thamirislibard/thrust-stand-calibration/src/0.Images/electromagnet_damping_34V_closer.png

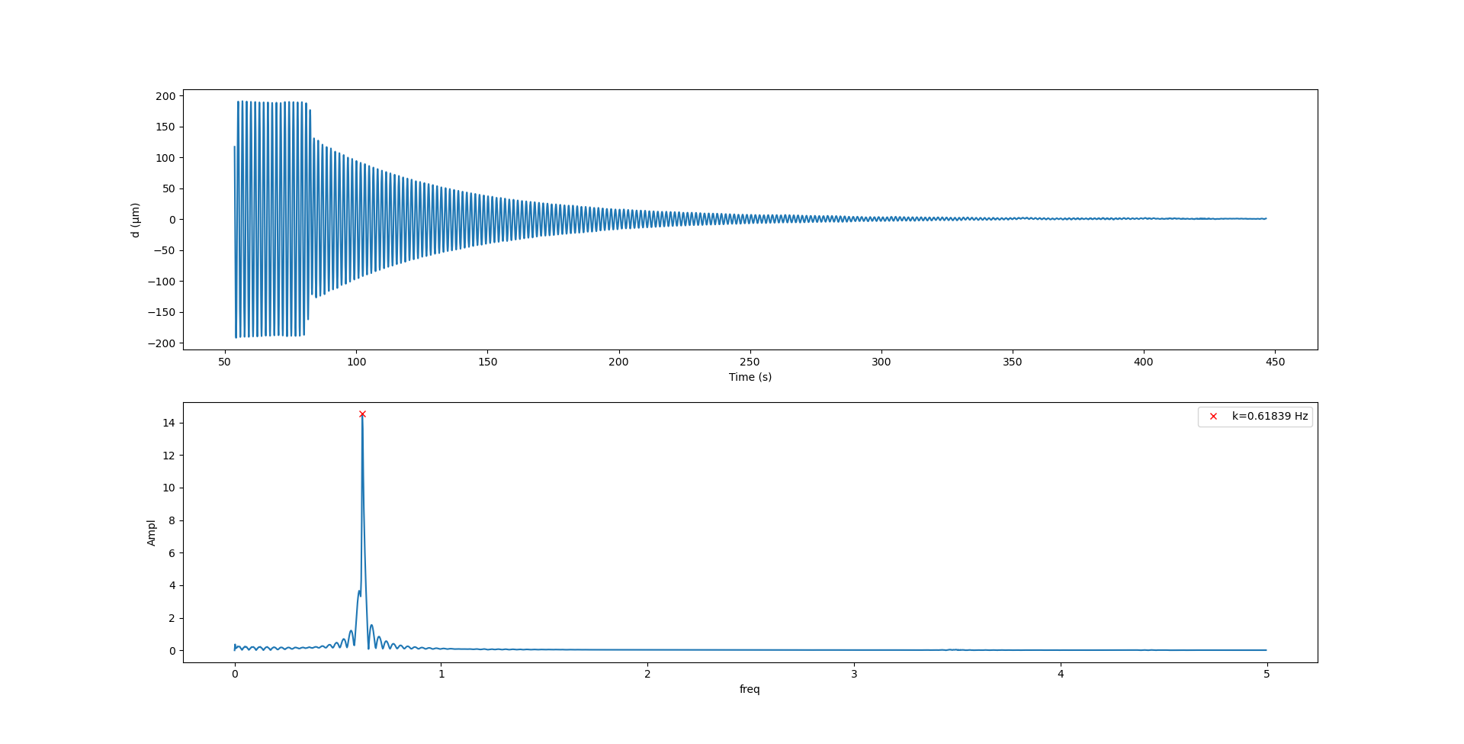
src/0.Images/electromagnet_damping_34V_closer.png
