thamirislibard/thrust-stand-calibration/src/0.Images/electromagnet_damping_34V_evencloser_2.png

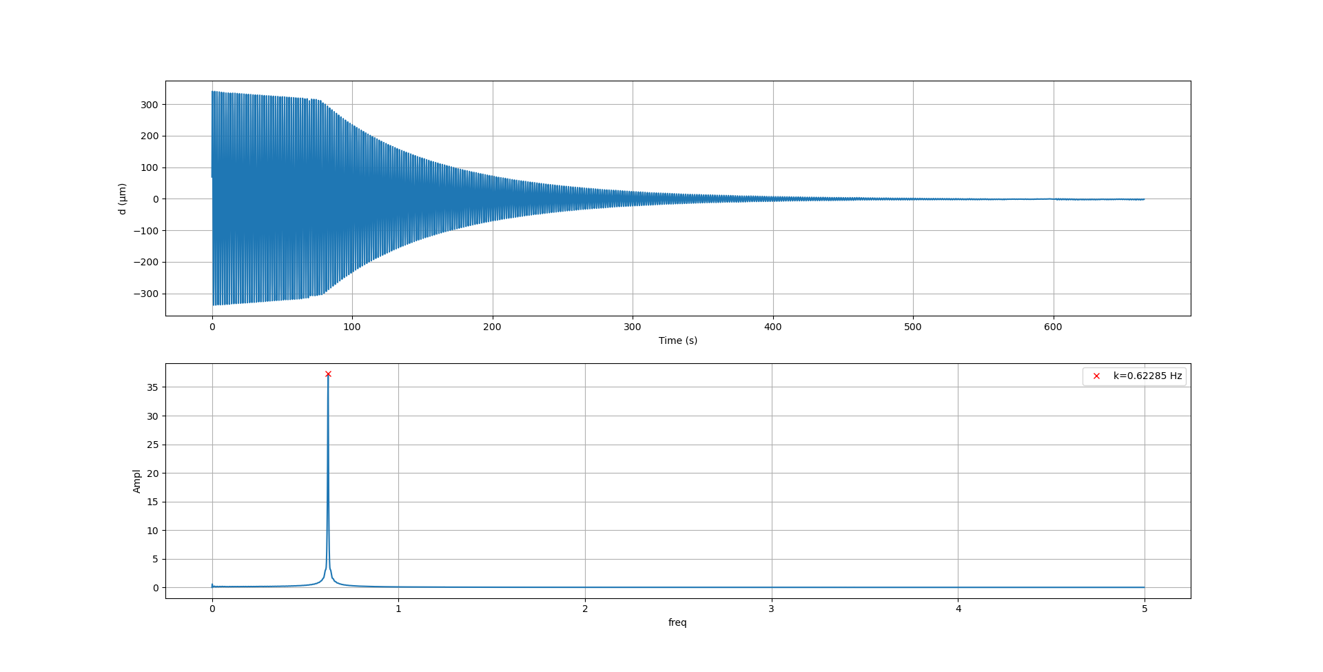
src/0.Images/electromagnet_damping_34V_evencloser_2.png
