thamirislibard/thrust-stand-calibration/src/0.Images/Static_deflection1_5mm.png

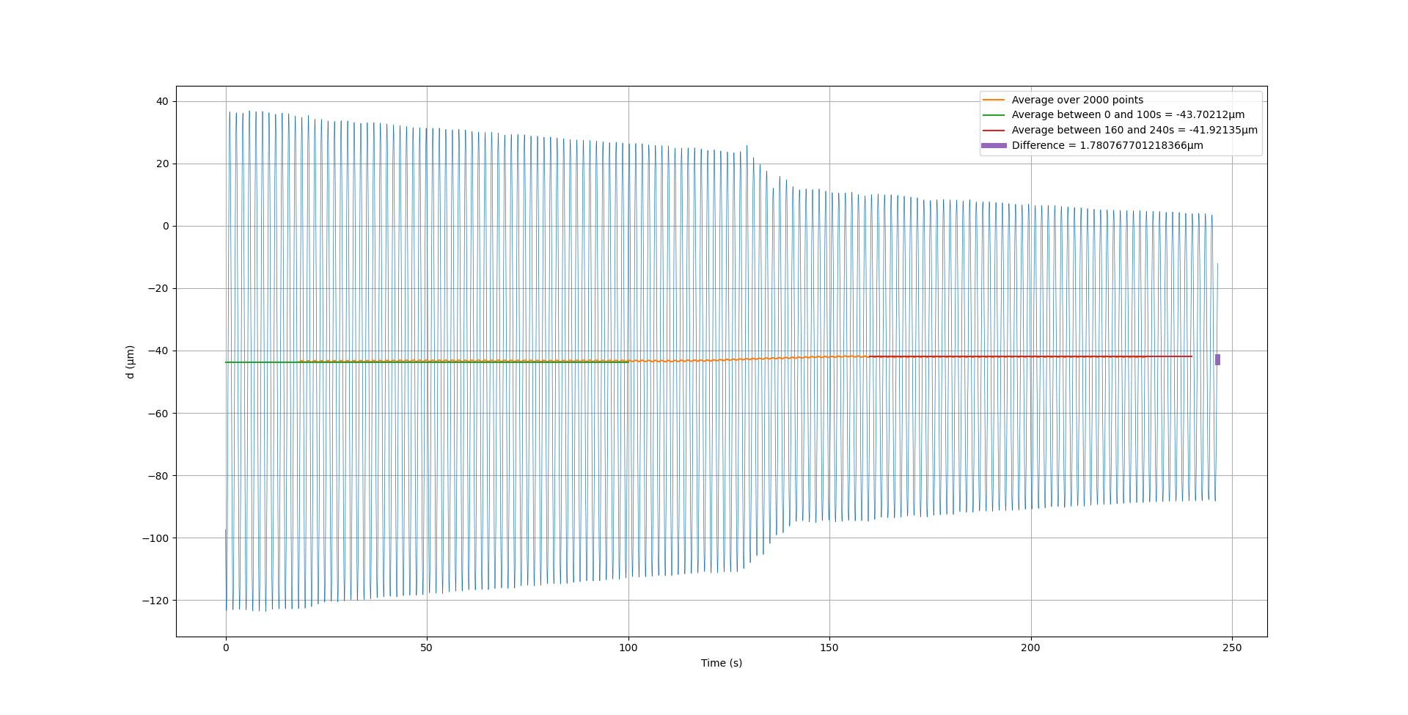
src/0.Images/Static_deflection1_5mm.png
