thamirislibard/thrust-stand-calibration/src/0.Images/Static_deflection1_15mm.png

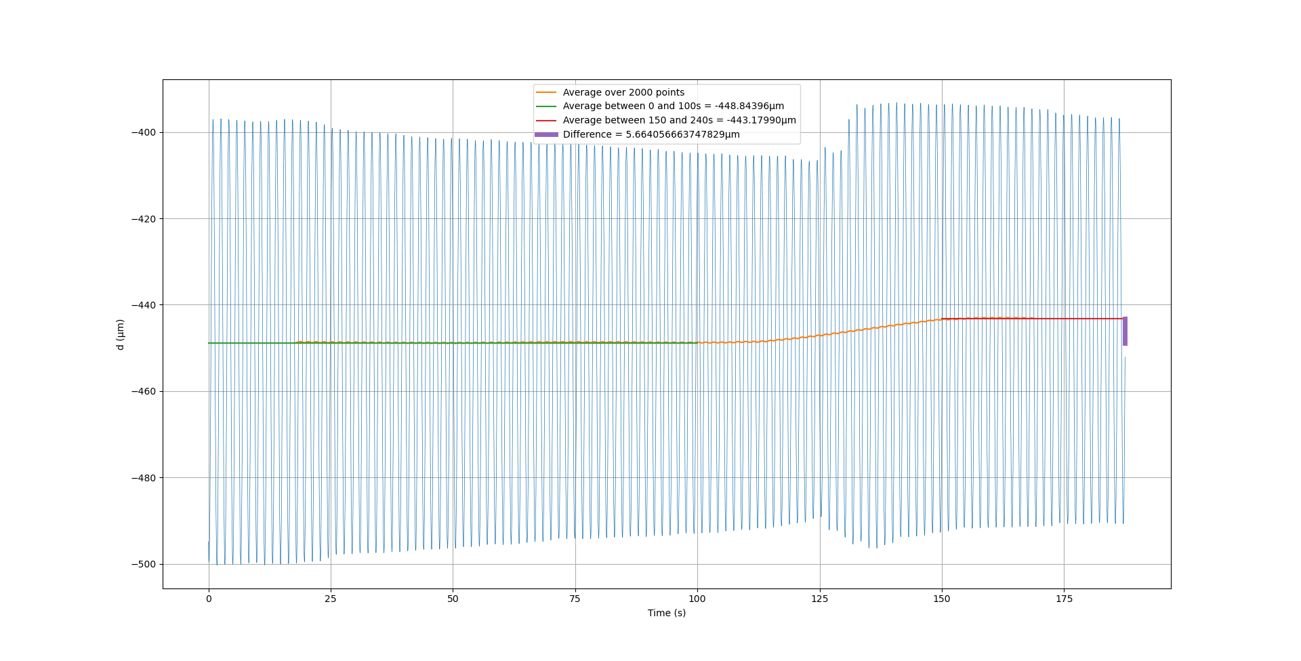
src/0.Images/Static_deflection1_15mm.png
