thamirislibard/thrust-stand-calibration/src/0.Images/Static_deflection.png

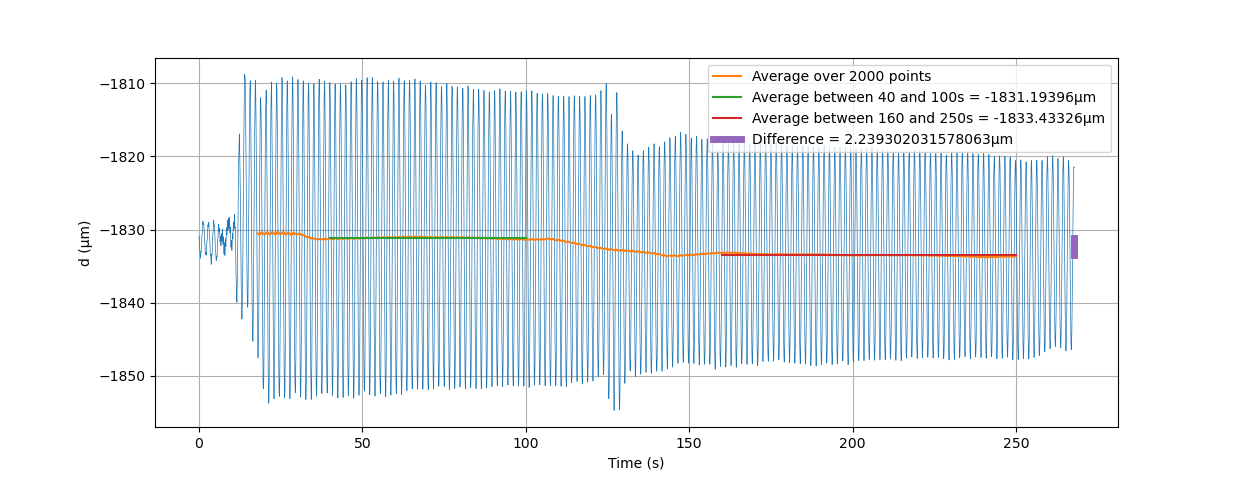
src/0.Images/Static_deflection.png
