thamirislibard/thrust-stand-calibration/src/0.Images/transversemode_nofiltering.png

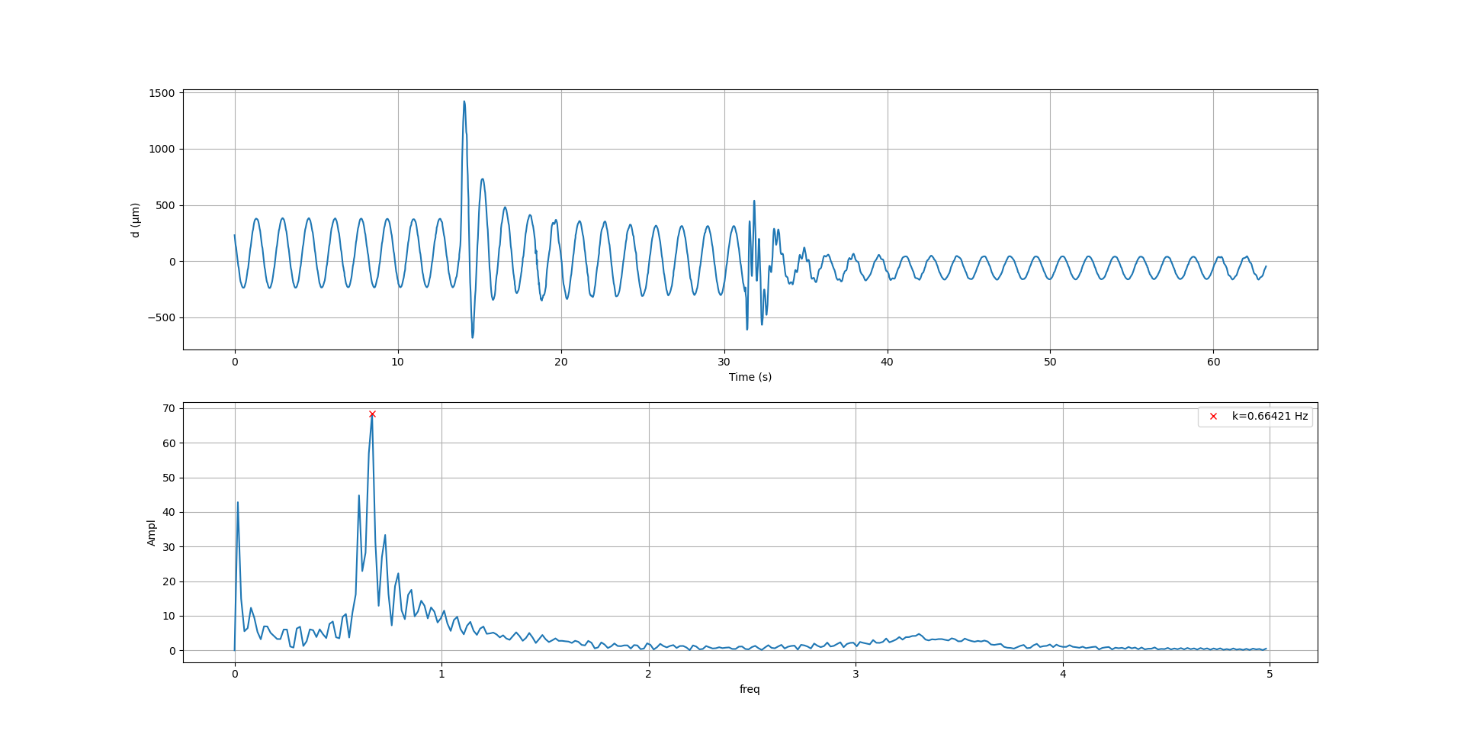
src/0.Images/transversemode_nofiltering.png
