thamirislibard/thrust-stand-calibration/data/Calibration Data/1.caldata_m4_l5_F9,725.png

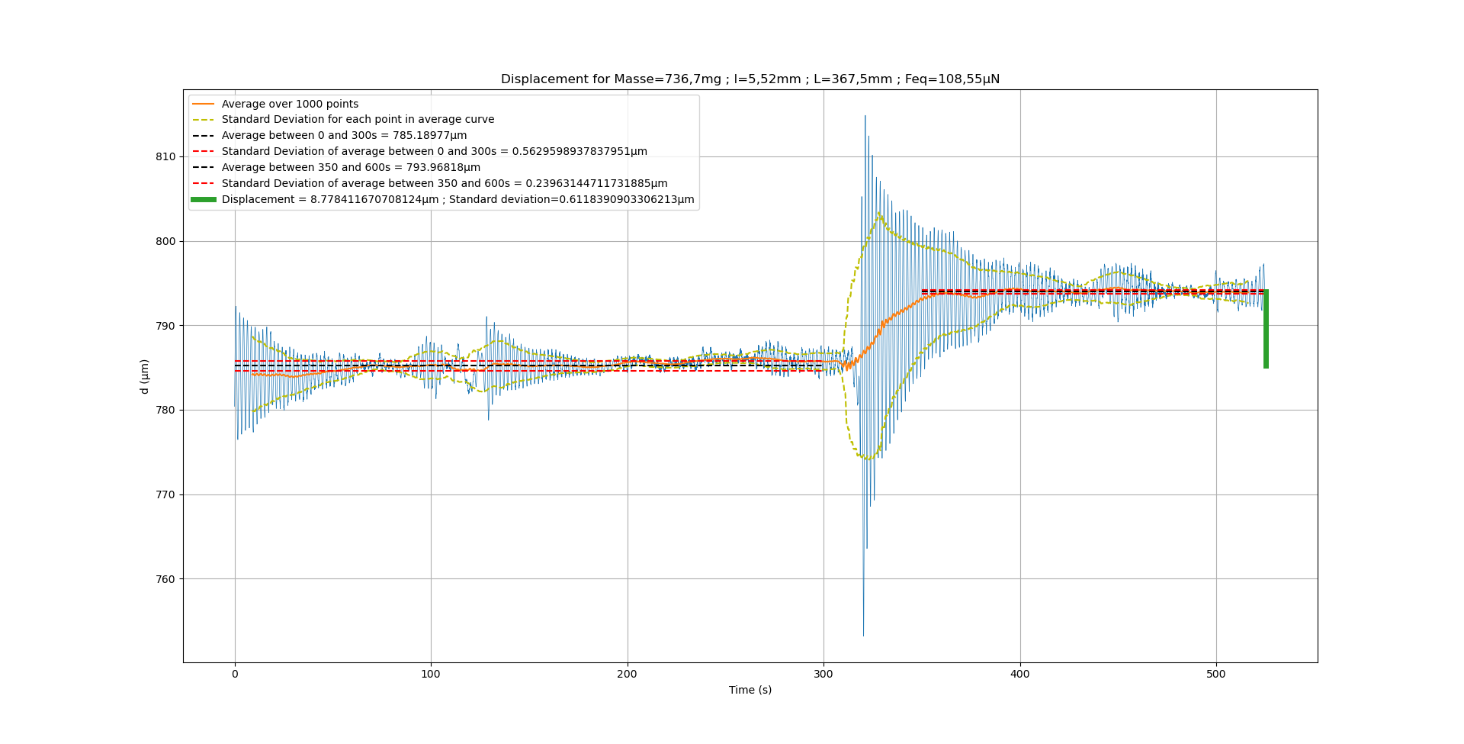
data/Calibration Data/1.caldata_m4_l5_F9,725.png
